GarablueX/Signal-Conditioning-System/images/Front full.PNG

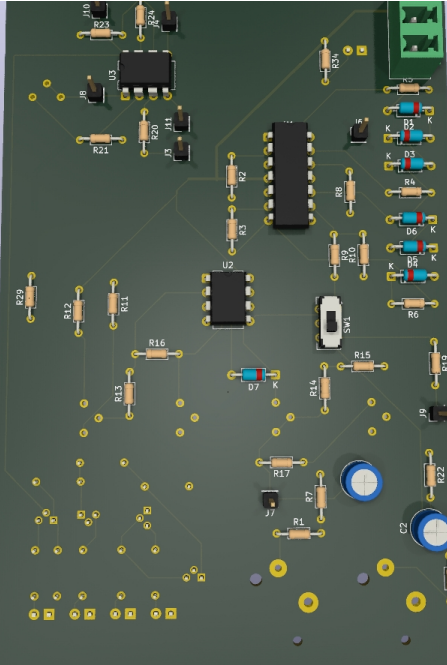
images/Front full.PNG
