GarablueX/Signal-Conditioning-System/images/image2.png

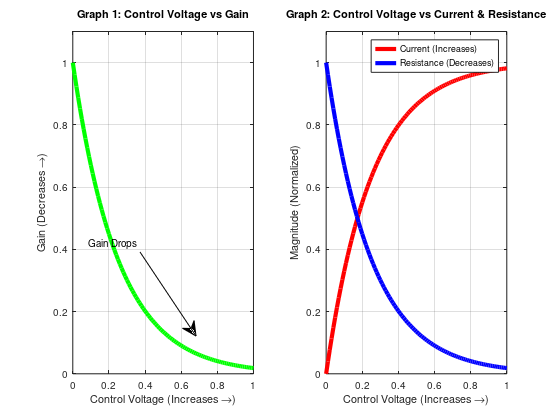
images/image2.png
