GarablueX/Signal-Conditioning-System/images/image4.png

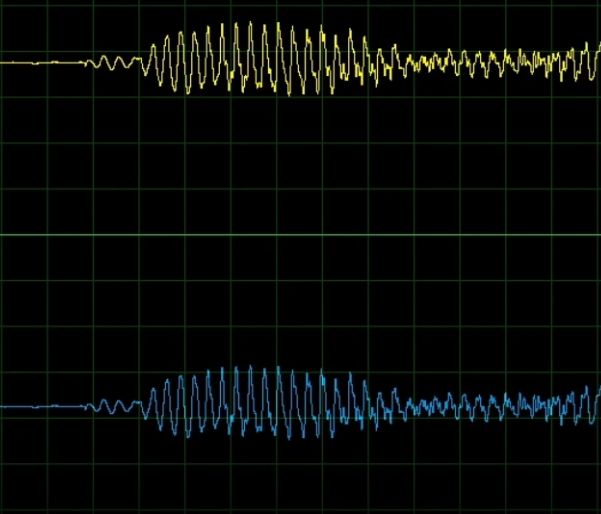
images/image4.png
