GarablueX/Signal-Conditioning-System/images/image5.png

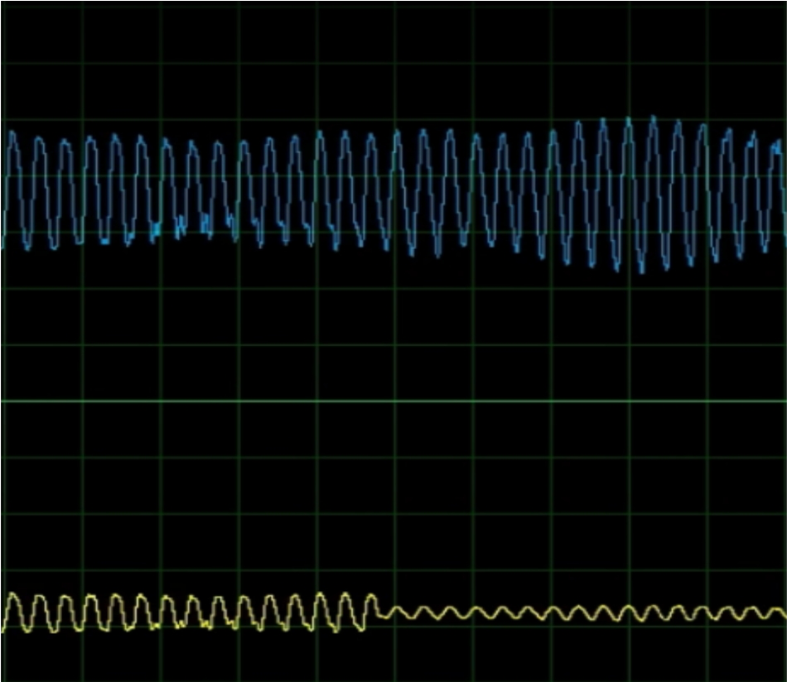
images/image5.png
