GarablueX/Signal-Conditioning-System/images/image8.png

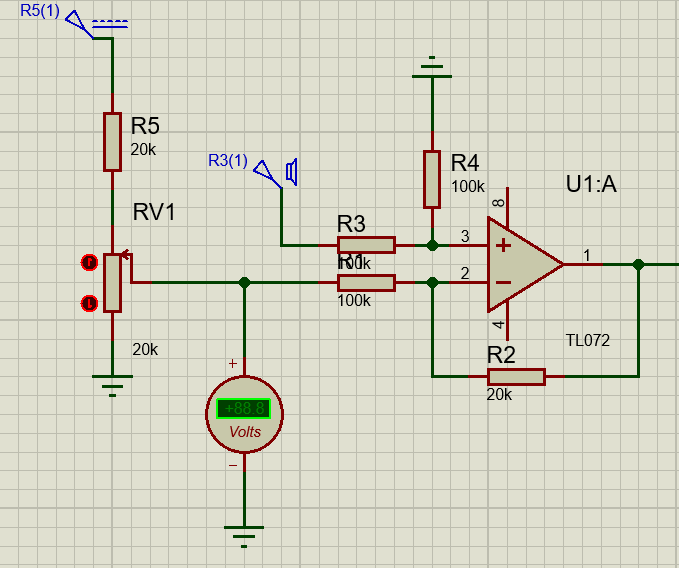
images/image8.png
