GarablueX/Signal-Conditioning-System/images/image10.png

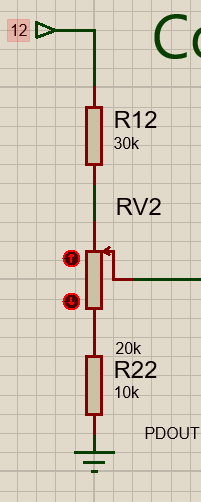
images/image10.png
