GarablueX/Signal-Conditioning-System/images/image12.png

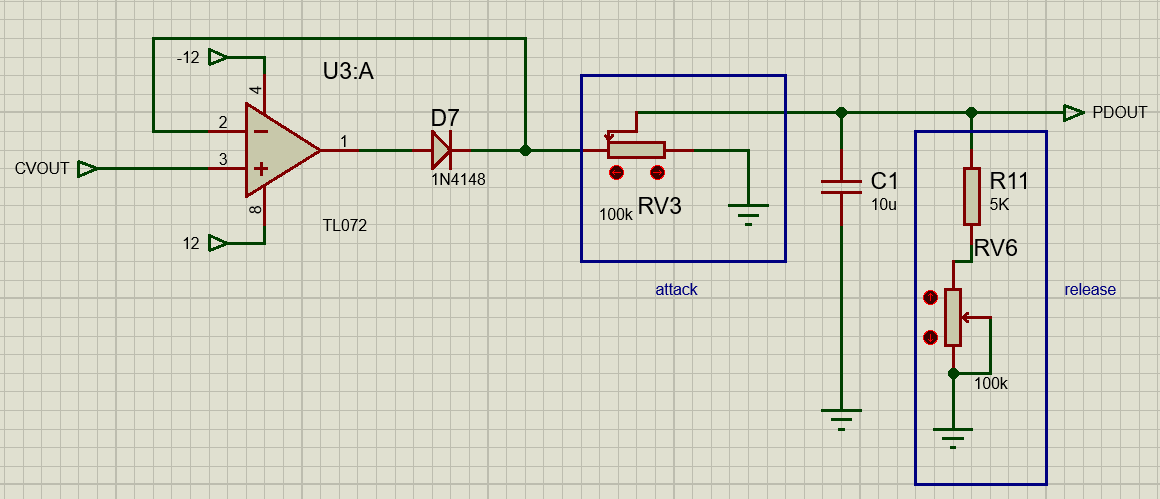
images/image12.png
