GarablueX/Signal-Conditioning-System/images/image16.png

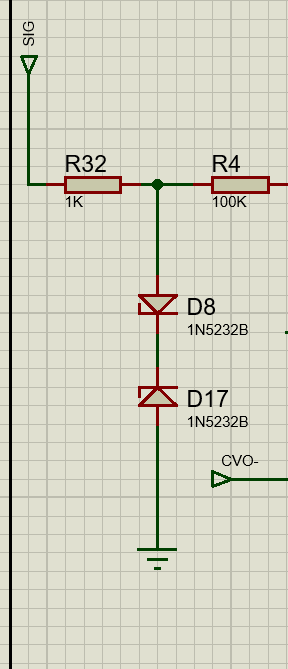
images/image16.png
