GarablueX/Signal-Conditioning-System/images/image23.png

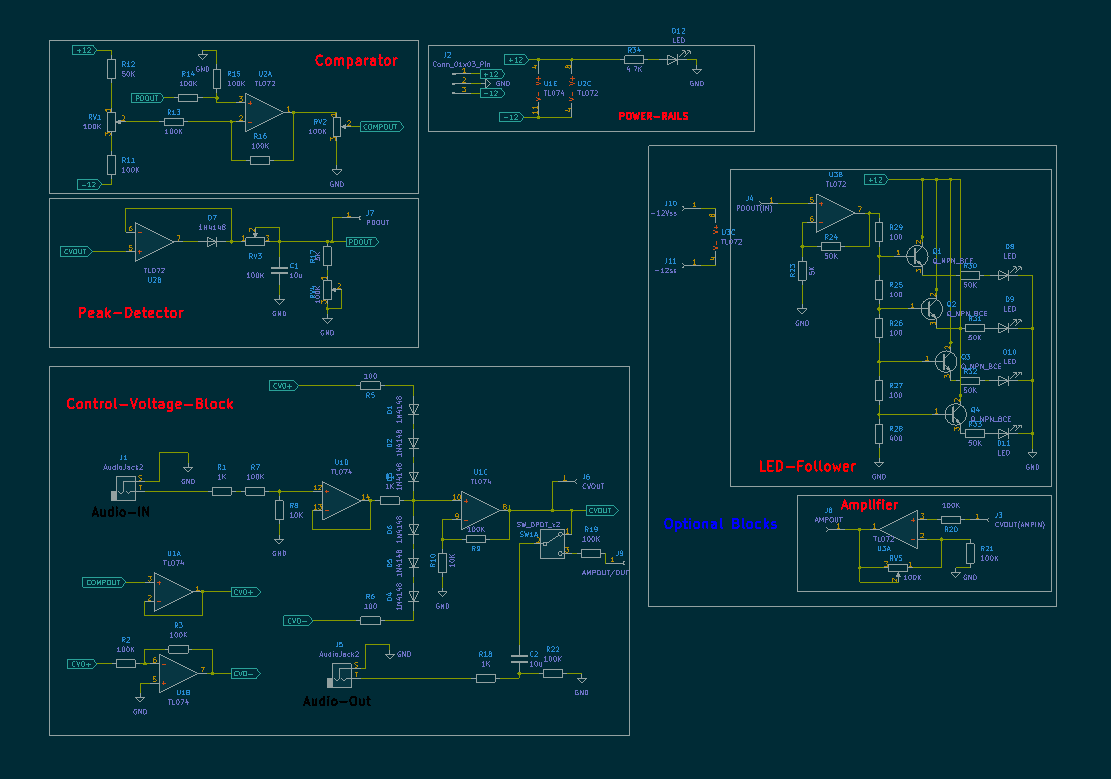
images/image23.png
