GarablueX/Signal-Conditioning-System/Schematics in KiCad/schematics(Pics)/LED-Follower.PNG

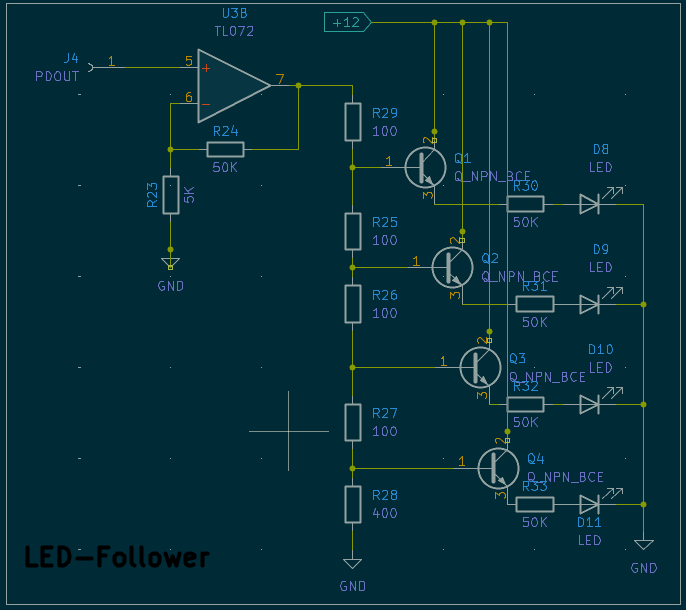
Schematics in KiCad/schematics(Pics)/LED-Follower.PNG
