GarablueX/Signal-Conditioning-System/Schematics in KiCad/schematics(Pics)/Power Rails.PNG

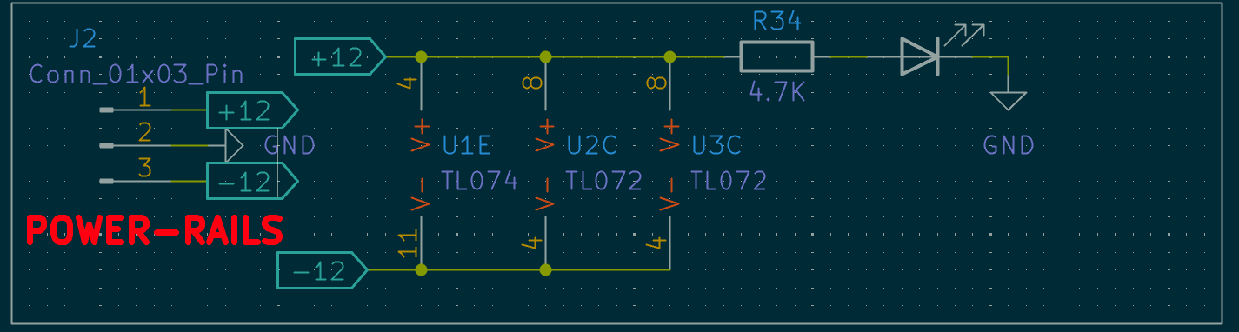
Schematics in KiCad/schematics(Pics)/Power Rails.PNG
