GarablueX/Signal-Conditioning-System/Topologys/Architecture.PNG

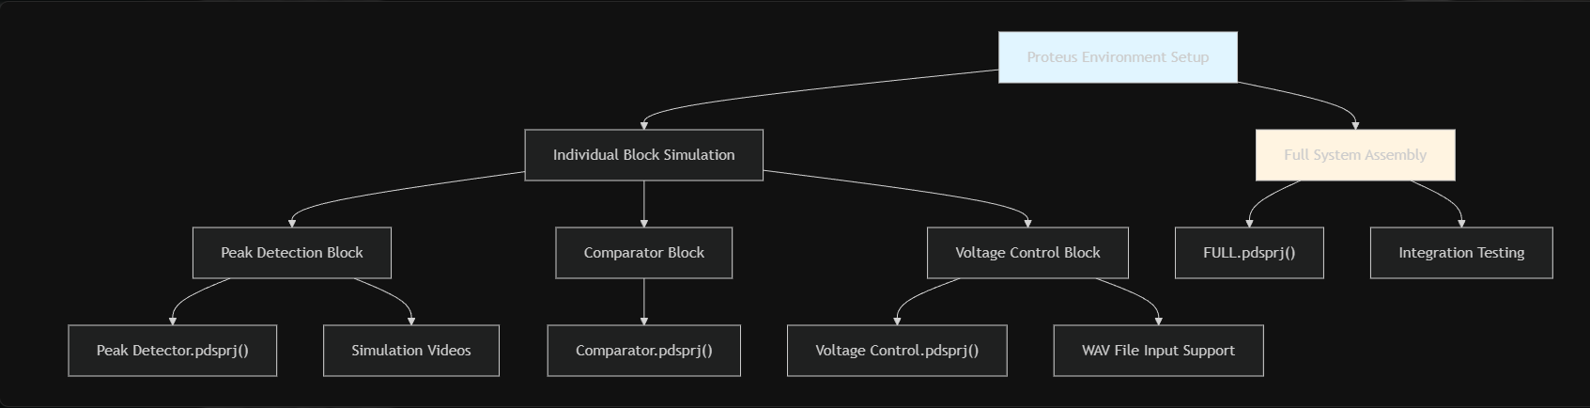
Topologys/Architecture.PNG
