GarablueX/Signal-Conditioning-System/Topologys/Signal Flow.PNG

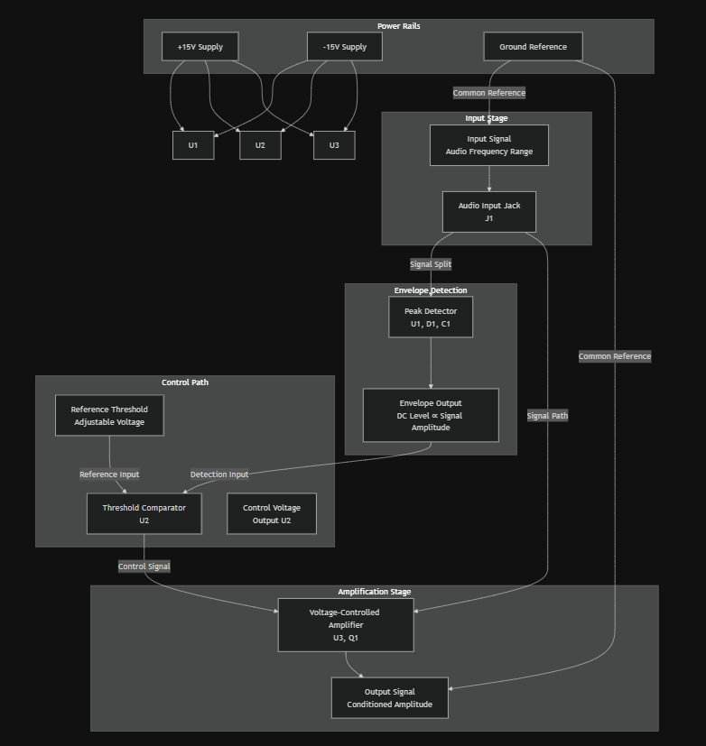
Topologys/Signal Flow.PNG
