GarablueX/Signal-Conditioning-System/Schematics(for simulation)/Assembly/Pics/1.PNG

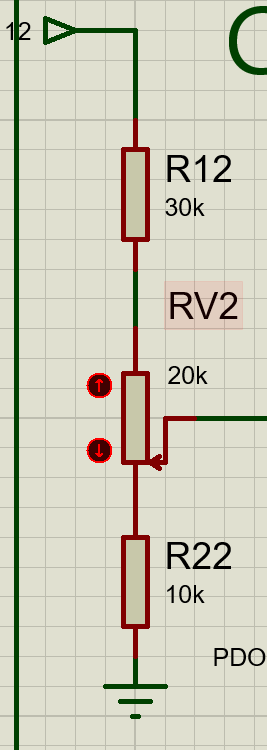
Schematics(for simulation)/Assembly/Pics/1.PNG
