GarablueX/Signal-Conditioning-System/Schematics(for simulation)/Assembly/Pics/Assembly.PNG

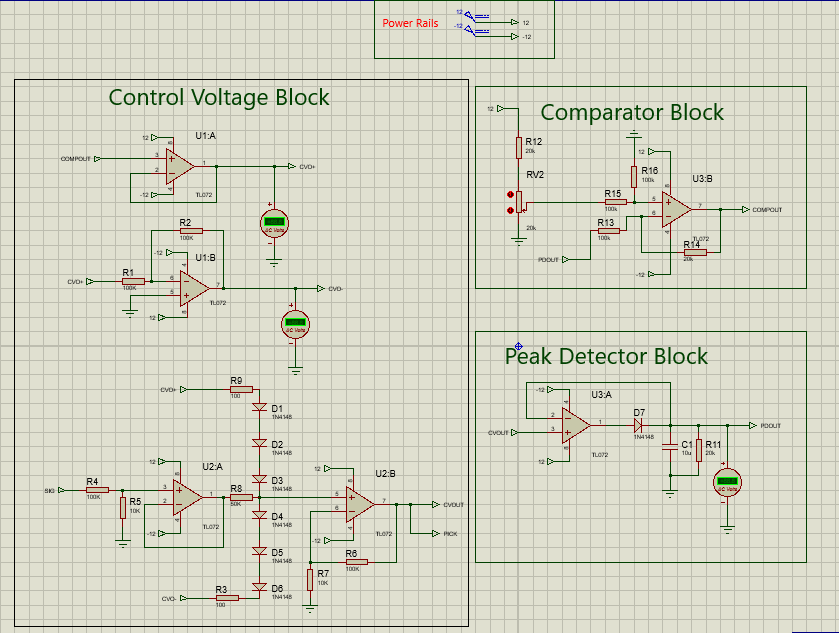
Schematics(for simulation)/Assembly/Pics/Assembly.PNG
